tl5915/Dive-Computer/data/image.jpg

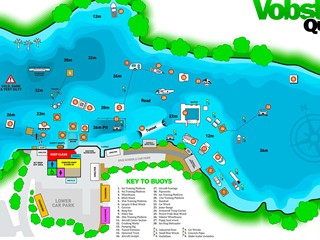
data/image.jpg
