tl5915/Dive-Computer/References/libbuhlmann/include/LibTypes.hpp

//
// Created by guyfleeman on 10/17/2020.
//

#ifndef LIBBUHLMAN_LIBTYPES_HPP
#define LIBBUHLMAN_LIBTYPES_HPP

typedef unsigned long int DiveTime_s;
typedef unsigned long int DiveTime_m;

#endif //LIBBUHLMAN_LIBTYPES_HPP
