tl5915/Dive-Computer/References/ESP32-S3-LCD-2-Demo/examples/09_lvgl_camera/09_lvgl_camera.ino

/*Using LVGL with Arduino requires some extra steps:
 *Be sure to read the docs here: https://docs.lvgl.io/master/get-started/platforms/arduino.html  */
#include "esp_camera.h"
#include <lvgl.h>
#include <Arduino_GFX_Library.h>
/*To use the built-in examples and demos of LVGL uncomment the includes below respectively.
 *You also need to copy `lvgl/examples` to `lvgl/src/examples`. Similarly for the demos `lvgl/demos` to `lvgl/src/demos`.
 Note that the `lv_examples` library is for LVGL v7 and you shouldn't install it for this version (since LVGL v8)
 as the examples and demos are now part of the main LVGL library. */

// #include <examples/lv_examples.h>
// #include <demos/lv_demos.h>

#define PWDN_GPIO_NUM 17   //power down is not used
#define RESET_GPIO_NUM -1  //software reset will be performed
#define XCLK_GPIO_NUM 8
#define SIOD_GPIO_NUM 21
#define SIOC_GPIO_NUM 16

#define Y9_GPIO_NUM 2
#define Y8_GPIO_NUM 7
#define Y7_GPIO_NUM 10
#define Y6_GPIO_NUM 14
#define Y5_GPIO_NUM 11
#define Y4_GPIO_NUM 15
#define Y3_GPIO_NUM 13
#define Y2_GPIO_NUM 12
#define VSYNC_GPIO_NUM 6
#define HREF_GPIO_NUM 4
#define PCLK_GPIO_NUM 9



#define EXAMPLE_PIN_NUM_LCD_SCLK 39
#define EXAMPLE_PIN_NUM_LCD_MOSI 38
#define EXAMPLE_PIN_NUM_LCD_MISO 40
#define EXAMPLE_PIN_NUM_LCD_DC 42
#define EXAMPLE_PIN_NUM_LCD_RST -1
#define EXAMPLE_PIN_NUM_LCD_CS 45
#define EXAMPLE_PIN_NUM_LCD_BL 1
#define EXAMPLE_PIN_NUM_TP_SDA 48
#define EXAMPLE_PIN_NUM_TP_SCL 47

#define LEDC_FREQ 5000
#define LEDC_TIMER_10_BIT 10

#define EXAMPLE_LCD_ROTATION 0
#define EXAMPLE_LCD_H_RES 240
#define EXAMPLE_LCD_V_RES 320


/* More data bus class: https://github.com/moononournation/Arduino_GFX/wiki/Data-Bus-Class */
Arduino_DataBus *bus = new Arduino_ESP32SPI(
  EXAMPLE_PIN_NUM_LCD_DC /* DC */, EXAMPLE_PIN_NUM_LCD_CS /* CS */,
  EXAMPLE_PIN_NUM_LCD_SCLK /* SCK */, EXAMPLE_PIN_NUM_LCD_MOSI /* MOSI */, EXAMPLE_PIN_NUM_LCD_MISO /* MISO */);

/* More display class: https://github.com/moononournation/Arduino_GFX/wiki/Display-Class */
Arduino_GFX *gfx = new Arduino_ST7789(
  bus, EXAMPLE_PIN_NUM_LCD_RST /* RST */, EXAMPLE_LCD_ROTATION /* rotation */, true /* IPS */,
  EXAMPLE_LCD_H_RES /* width */, EXAMPLE_LCD_V_RES /* height */);


/*******************************************************************************
 * End of Arduino_GFX setting
 ******************************************************************************/

/*******************************************************************************
 * Please config the touch panel in touch.h
 ******************************************************************************/
// #include "touch.h"

uint32_t screenWidth;
uint32_t screenHeight;
uint32_t bufSize;
lv_disp_draw_buf_t draw_buf;
lv_color_t *disp_draw_buf;
lv_disp_drv_t disp_drv;

static SemaphoreHandle_t lvgl_api_mux = NULL;

lv_obj_t *img_camera;



bool lvgl_lock(int timeout_ms) {
  // Convert timeout in milliseconds to FreeRTOS ticks
  // If `timeout_ms` is set to -1, the program will block until the condition is met
  const TickType_t timeout_ticks = (timeout_ms == -1) ? portMAX_DELAY : pdMS_TO_TICKS(timeout_ms);
  return xSemaphoreTakeRecursive(lvgl_api_mux, timeout_ticks) == pdTRUE;
}

void lvgl_unlock(void) {
  xSemaphoreGiveRecursive(lvgl_api_mux);
}


#if LV_USE_LOG != 0
/* Serial debugging */
void my_print(const char *buf) {
  Serial.printf(buf);
  Serial.flush();
}
#endif

/* Display flushing */
void my_disp_flush(lv_disp_drv_t *disp_drv, const lv_area_t *area, lv_color_t *color_p) {
#if (LV_COLOR_16_SWAP != 0)
  gfx->draw16bitBeRGBBitmap(0, 0, (uint16_t *)disp_draw_buf, screenWidth, screenHeight);
#else
  gfx->draw16bitRGBBitmap(0, 0, (uint16_t *)disp_draw_buf, screenWidth, screenHeight);
#endif
  lv_disp_flush_ready(disp_drv);
}




void lvgl_camera_ui_init(lv_obj_t *parent) {
  // lv_obj_t *obj = lv_obj_create(parent);
  // lv_obj_set_size(obj, lv_pct(100), lv_pct(100));
  img_camera = lv_img_create(parent);
  // lv_obj_set_size(img_camera, 240,);
  // lv_img_set_angle(img_camera, 900);
  lv_obj_align(img_camera, LV_ALIGN_CENTER, 0, 0);  // 居中显示
  lv_obj_set_pos(img_camera, -1, 0);
  lv_obj_set_scroll_dir(parent, LV_DIR_NONE);

  lv_obj_set_style_pad_top(img_camera, 0, LV_PART_MAIN);
  lv_obj_set_style_pad_bottom(img_camera, 0, LV_PART_MAIN);
  lv_obj_set_style_pad_left(img_camera, 0, LV_PART_MAIN);
  lv_obj_set_style_pad_right(img_camera, 0, LV_PART_MAIN);
}


static void task(void *param) {
  camera_config_t config;
  config.ledc_channel = LEDC_CHANNEL_0;
  config.ledc_timer = LEDC_TIMER_1;
  config.pin_d0 = Y2_GPIO_NUM;
  config.pin_d1 = Y3_GPIO_NUM;
  config.pin_d2 = Y4_GPIO_NUM;
  config.pin_d3 = Y5_GPIO_NUM;
  config.pin_d4 = Y6_GPIO_NUM;
  config.pin_d5 = Y7_GPIO_NUM;
  config.pin_d6 = Y8_GPIO_NUM;
  config.pin_d7 = Y9_GPIO_NUM;
  config.pin_xclk = XCLK_GPIO_NUM;
  config.pin_pclk = PCLK_GPIO_NUM;
  config.pin_vsync = VSYNC_GPIO_NUM;
  config.pin_href = HREF_GPIO_NUM;
  config.pin_sccb_sda = SIOD_GPIO_NUM;
  config.pin_sccb_scl = SIOC_GPIO_NUM;
  config.pin_pwdn = PWDN_GPIO_NUM;
  config.pin_reset = RESET_GPIO_NUM;
  config.xclk_freq_hz = 20000000;
  config.frame_size = FRAMESIZE_HVGA;
  config.pixel_format = PIXFORMAT_RGB565;  // for streaming
  //config.pixel_format = PIXFORMAT_RGB565; // for face detection/recognition
  config.grab_mode = CAMERA_GRAB_WHEN_EMPTY;
  config.fb_location = CAMERA_FB_IN_PSRAM;
  config.jpeg_quality = 12;
  config.fb_count = 1;

  esp_err_t err = esp_camera_init(&config);
  if (err != ESP_OK) {
    Serial.printf("Camera init failed with error 0x%x", err);
    vTaskDelete(NULL);
    return;
  }

  sensor_t * s = esp_camera_sensor_get();
  s->set_hmirror(s, 1);

  camera_fb_t *pic;
  lv_img_dsc_t img_dsc;
  img_dsc.header.always_zero = 0;
  img_dsc.header.w = 480;
  img_dsc.header.h = 320;
  img_dsc.data_size = 320 * 480 * 2;
  img_dsc.header.cf = LV_IMG_CF_TRUE_COLOR;
  img_dsc.data = NULL;

  // lv_img_set_src(img_camera, &pic);
  while (1) {
    pic = esp_camera_fb_get();

    if (NULL != pic) {
      img_dsc.data = pic->buf;
      if (lvgl_lock(-1)) {
        lv_img_set_src(img_camera, &img_dsc);
        lvgl_unlock();
      }
    }
    esp_camera_fb_return(pic);
    vTaskDelay(pdMS_TO_TICKS(1));
  }
  vTaskDelete(NULL);
}


void setup() {
  Serial.begin(115200);
  lvgl_api_mux = xSemaphoreCreateRecursiveMutex();
  // Serial.setDebugOutput(true);
  // while(!Serial);
  Serial.println("Arduino_GFX LVGL_Arduino_v8 example ");
  String LVGL_Arduino = String('V') + lv_version_major() + "." + lv_version_minor() + "." + lv_version_patch();
  Serial.println(LVGL_Arduino);

#ifdef GFX_EXTRA_PRE_INIT
  GFX_EXTRA_PRE_INIT();
#endif

  // Init Display
  if (!gfx->begin()) {
    Serial.println("gfx->begin() failed!");
  }
  gfx->fillScreen(BLACK);

#ifdef EXAMPLE_PIN_NUM_LCD_BL
  ledcAttach(EXAMPLE_PIN_NUM_LCD_BL, LEDC_FREQ, LEDC_TIMER_10_BIT);
  ledcWrite(EXAMPLE_PIN_NUM_LCD_BL, (1 << LEDC_TIMER_10_BIT) / 100 * 80);
#endif

  // Init touch device
  // touch_init(gfx->width(), gfx->height(), gfx->getRotation());
  Wire.begin(EXAMPLE_PIN_NUM_TP_SDA, EXAMPLE_PIN_NUM_TP_SCL);
  lv_init();

#if LV_USE_LOG != 0
  lv_log_register_print_cb(my_print); /* register print function for debugging */
#endif

  screenWidth = gfx->width();
  screenHeight = gfx->height();

  bufSize = screenWidth * screenHeight;


  disp_draw_buf = (lv_color_t *)heap_caps_malloc(bufSize * 2, MALLOC_CAP_INTERNAL | MALLOC_CAP_8BIT);
  if (!disp_draw_buf) {
    // remove MALLOC_CAP_INTERNAL flag try again
    disp_draw_buf = (lv_color_t *)heap_caps_malloc(bufSize * 2, MALLOC_CAP_8BIT);
  }


  if (!disp_draw_buf) {
    Serial.println("LVGL disp_draw_buf allocate failed!");
  } else {
    lv_disp_draw_buf_init(&draw_buf, disp_draw_buf, NULL, bufSize);

    /* Initialize the display */
    lv_disp_drv_init(&disp_drv);
    /* Change the following line to your display resolution */
    disp_drv.hor_res = screenWidth;
    disp_drv.ver_res = screenHeight;
    disp_drv.flush_cb = my_disp_flush;
    disp_drv.draw_buf = &draw_buf;
    disp_drv.direct_mode = true;

    lv_disp_drv_register(&disp_drv);

    /* Option 3: Or try out a demo. Don't forget to enable the demos in lv_conf.h. E.g. LV_USE_DEMOS_WIDGETS*/
    lvgl_camera_ui_init(lv_scr_act());
    // lv_demo_widgets();
    // lv_demo_benchmark();
    // lv_demo_keypad_encoder();
    // lv_demo_music();
    // lv_demo_stress();
  }
  Serial.println("Setup done");
  xTaskCreatePinnedToCore(
    task,
    "lvgl_app_task",
    1024 * 10,
    NULL,
    1,
    NULL,
    0);
}

void loop() {
  if (lvgl_lock(-1)) {
    lv_timer_handler(); /* let the GUI do its work */
    lvgl_unlock();
  }
  vTaskDelay(pdMS_TO_TICKS(5));
}
